costarc/MSXPi/documents/Tutorial - Setup  Raspberry Pi for MSXPi the Hard Way - Installing Raspbian from Scratch.pdf

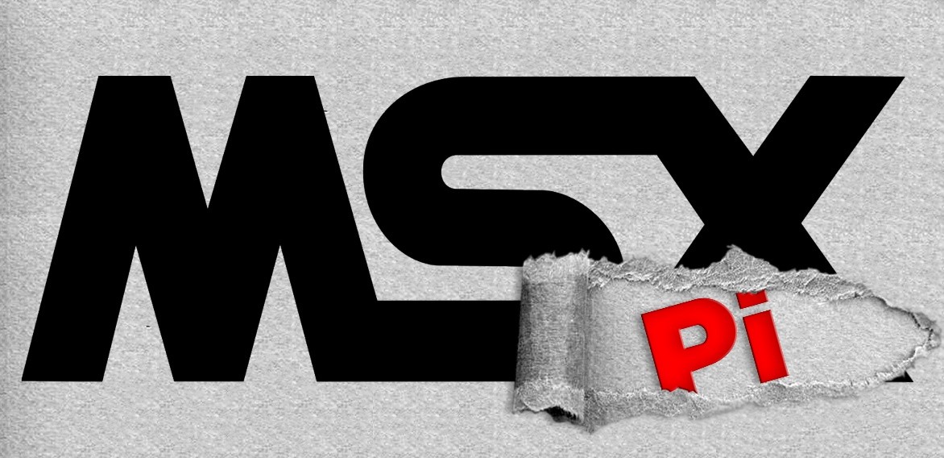
[picture p83: figure]

* This is a MSXPi Developer Contribution by Retropix Brazil * This tutorial will help you in a simple, direct and didactic way to prepare and install all the necessary software on the Micro SD card to use your MSXPi.

## Downloading the Installation Software for the Raspberry Pi OS

1st. Go to the link https://www.raspberrypi.com/software to download and run the software that will install the Raspberry Pi OS on your micro SD card.

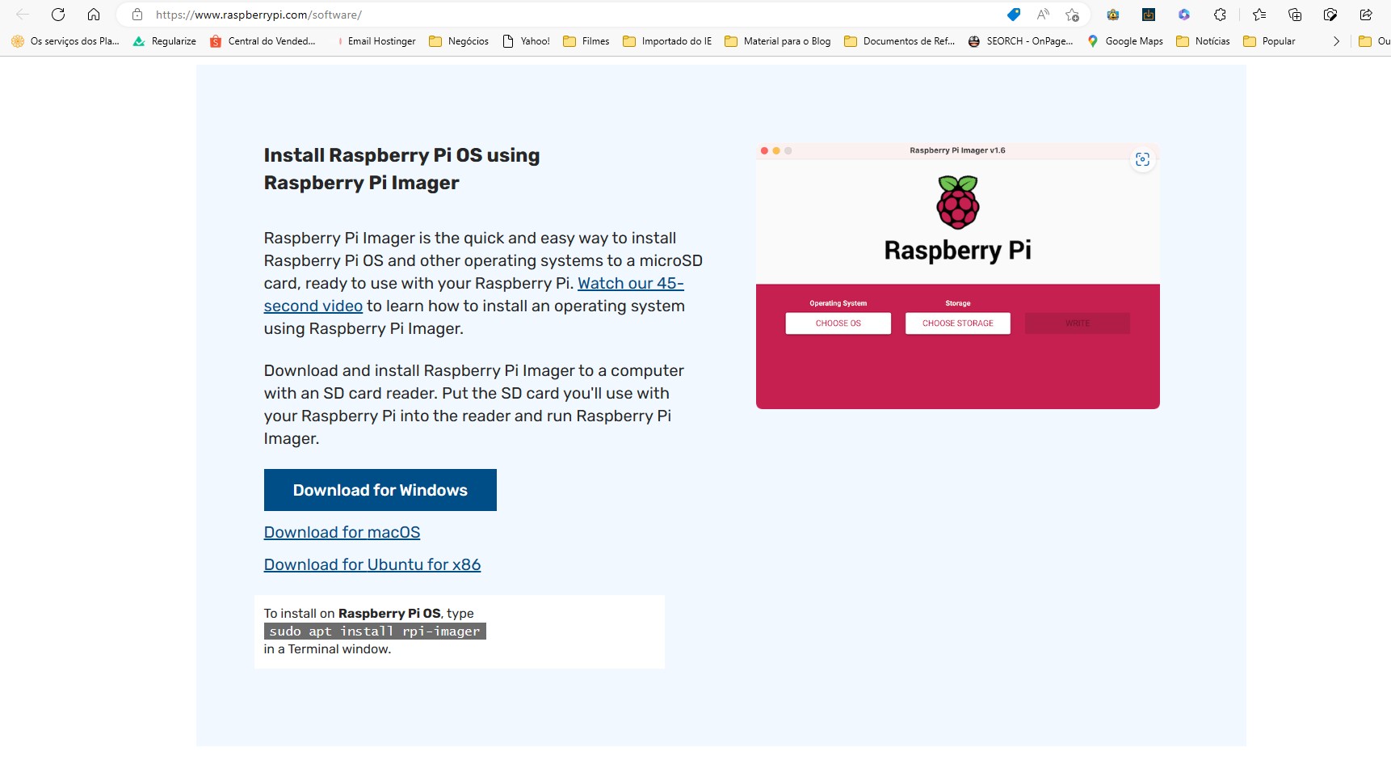
[picture p84: figure]

2nd. Download the installer for the platform that suits you best. The options are for Windows, macOS, and Ubuntu.
In this tutorial we will do the installation using Windows 10.
3rd. After downloading the imager_1.7.4.exe file (latest version) in your download area. Click on it to run.

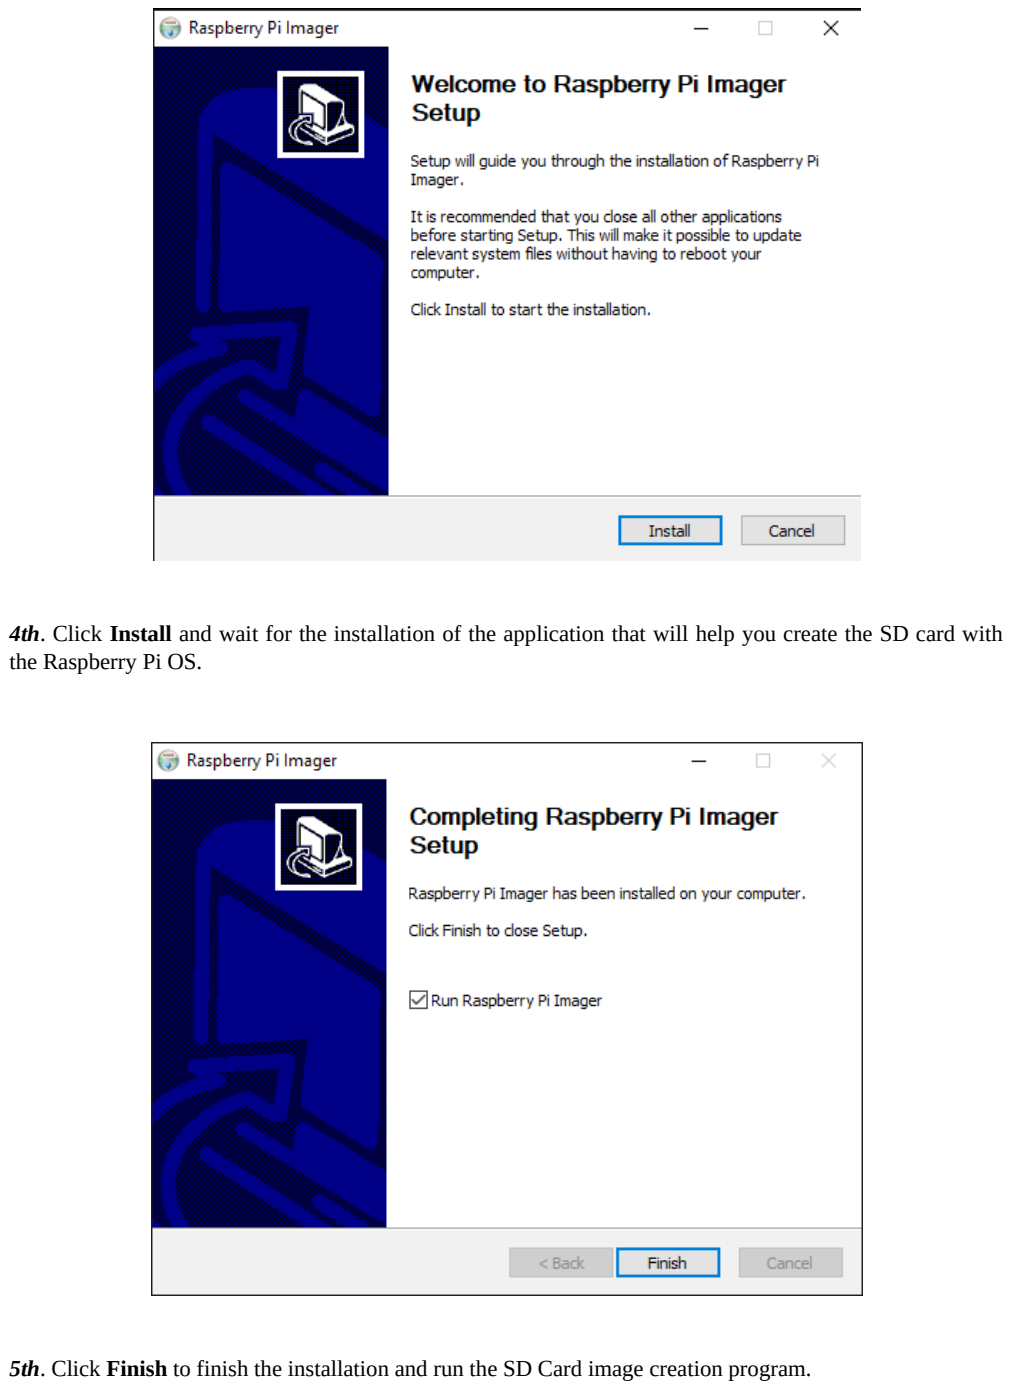
[picture p85: page 2]

4th. Click Install and wait for the installation of the application that will help you create the SD card with the Raspberry Pi OS.

5th. Click Finish to finish the installation and run the SD Card image creation program.

## Installing the Raspberry Pi OS System Properly

1st. Insert the Micro SD card you want to use into your Computer.

2nd. With the application open and the Micro SD card already inserted, first click on CHOOSE OS.


3rd. Choose the Raspberry Pi OS (Other) option to choose the version we use on the MSXPi.

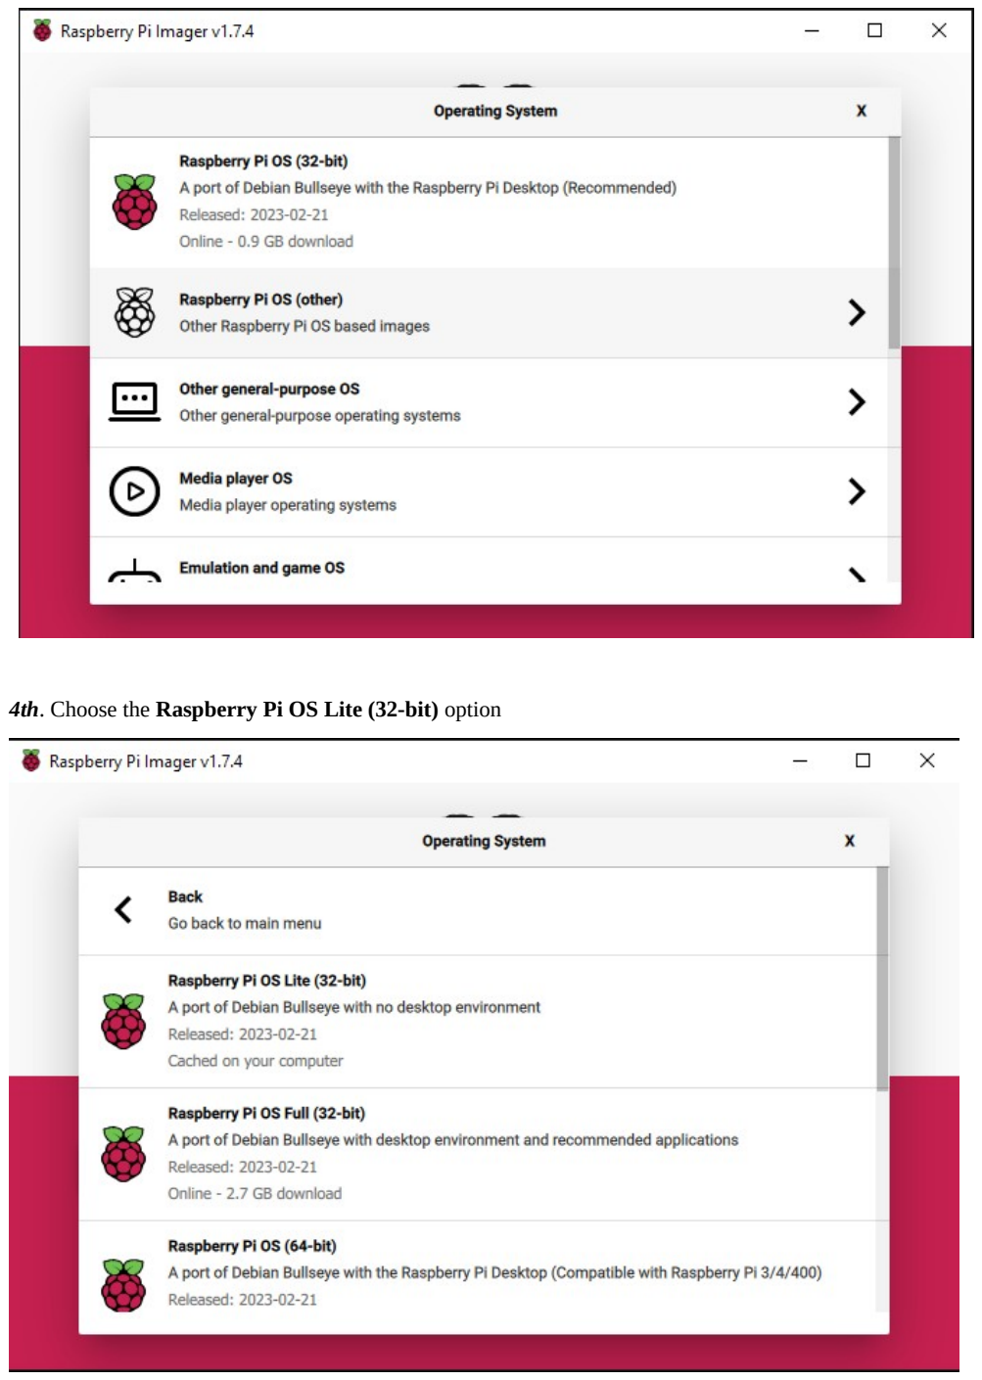
[picture p86: page 4]

4th. Choose the Raspberry Pi OS Lite (32-bit) option

5th. Now click on CHOOSE STORAGE button to choose your Micro SD card and install Raspberry Pi OS


6th. Click on the Gear button to configure the options for remote access in the Raspberry Pi OS via computer

7th. Check Set hostname

8th. Also check the option Enable SSH

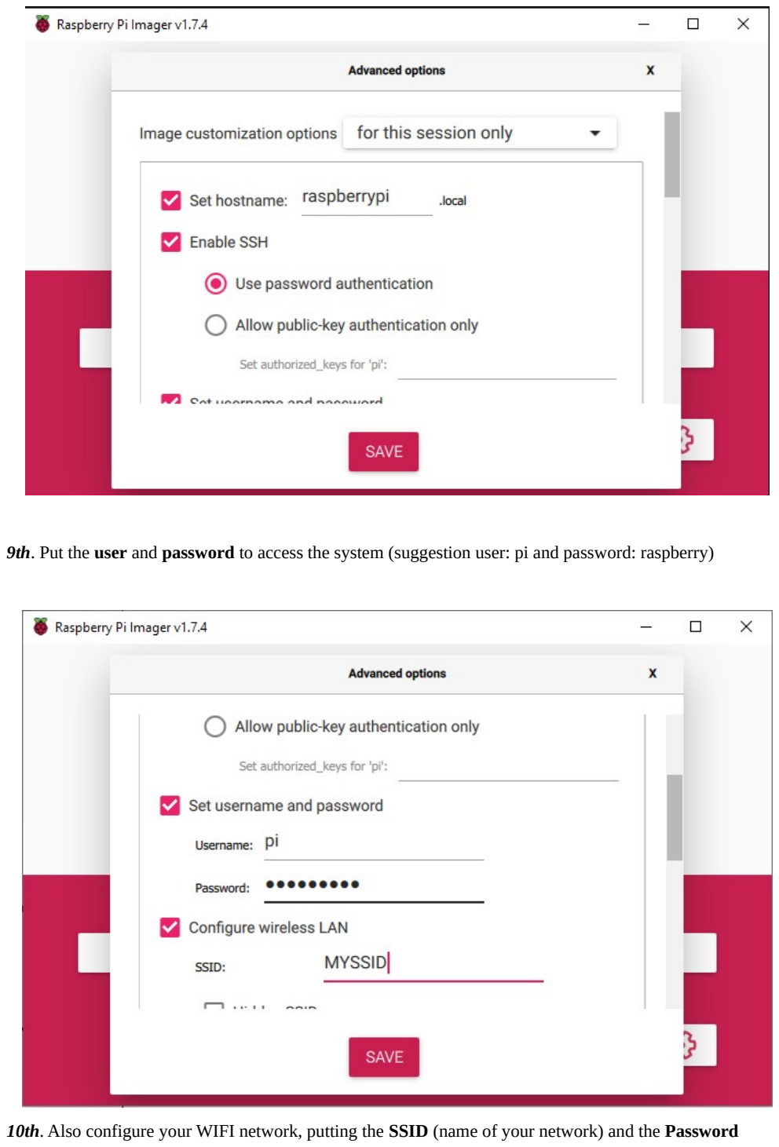
[picture p87: page 6]

9th. Put the user and password to access the system (suggestion user: pi and password: raspberry)

10th. Also configure your WIFI network, putting the SSID (name of your network) and the Password

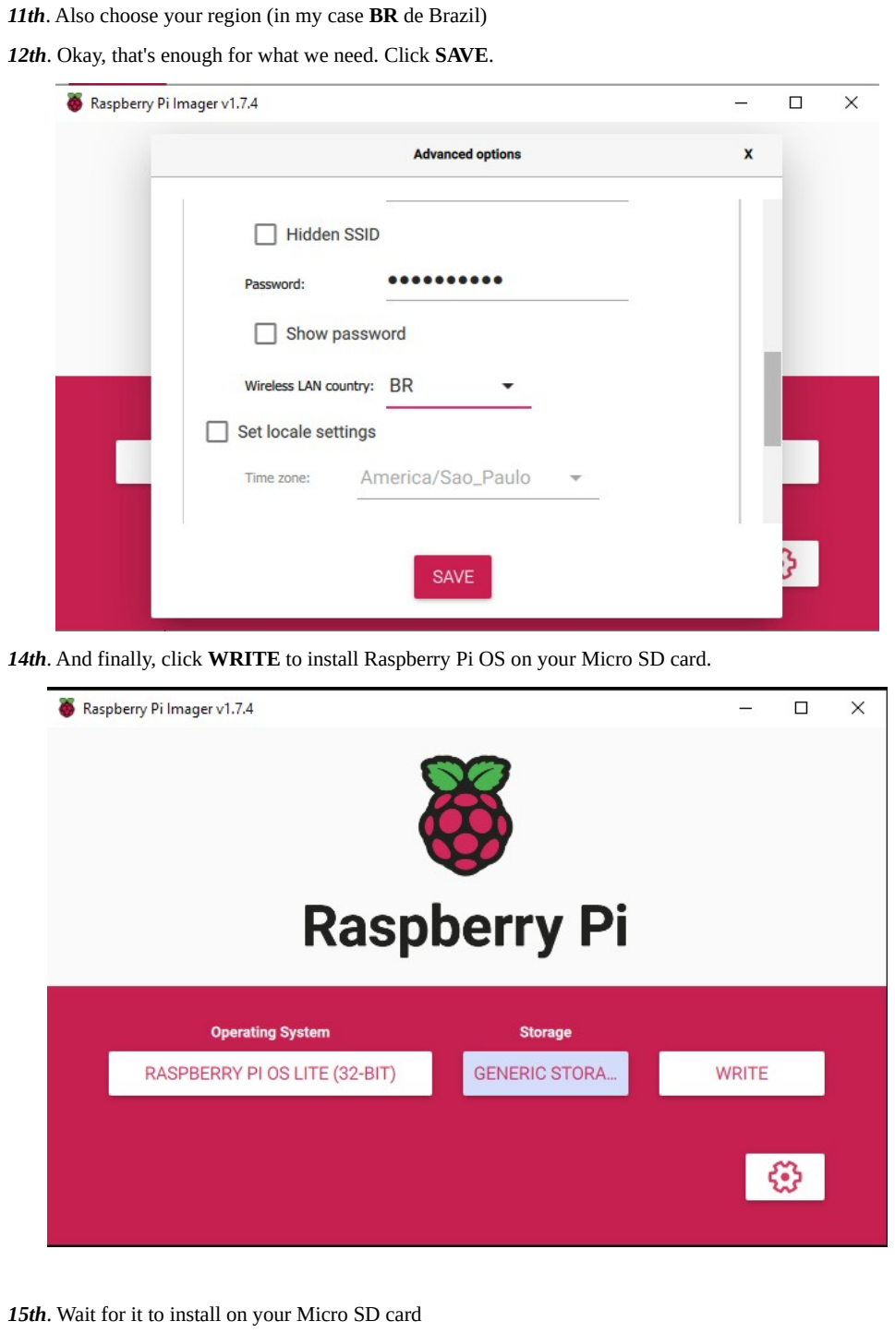
[picture p88: page 7]

11th. Also choose your region (in my case BR de Brazil) 12th. Okay, that's enough for what we need. Click SAVE.

14th. And finally, click WRITE to install Raspberry Pi OS on your Micro SD card.

15th. Wait for it to install on your Micro SD card

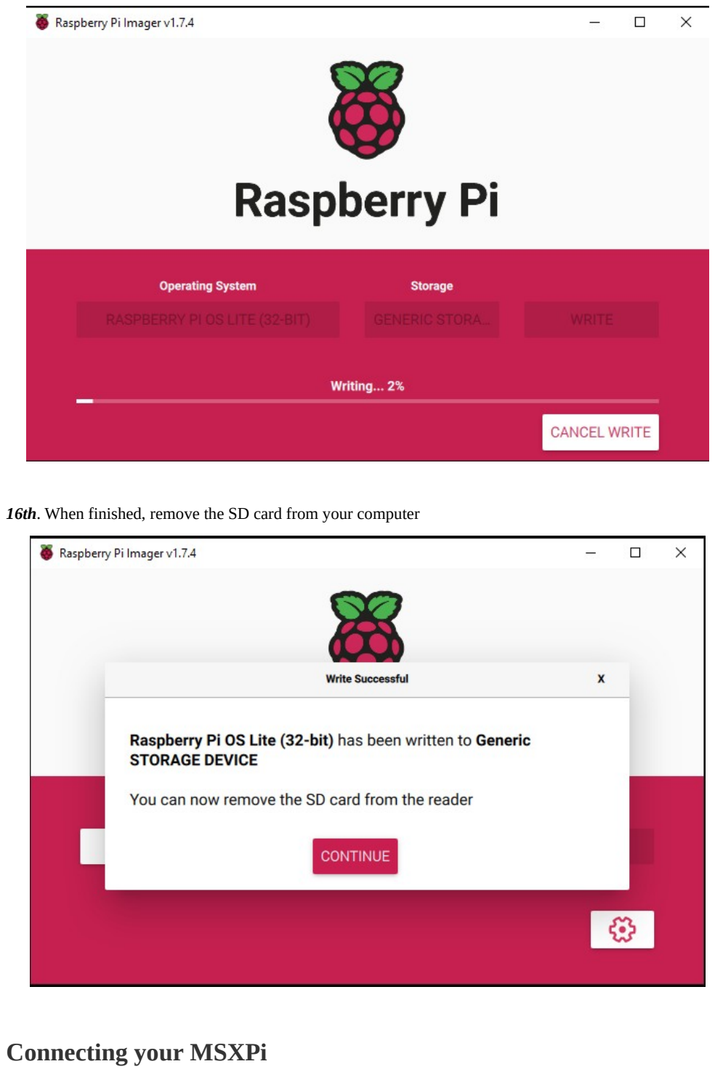
[picture p89: page 8]

16th. When finished, remove the SD card from your computer

## Connecting your MSXPi

Now, insert your Micro SD card into the MSXPi. Plug the MSXPi cartridge into your MSX and turn it on. Wait for all initialization to finish. At this point, MSXPi should be trying to connect to your WiFi network. After your MSXPi connects to your WiFi network (It takes a long time to connect to your network the first time, about 5-10 minutes). If you can, monitor your router by checking if the Raspberry has already connected or simply wait and test the connection through Putty.

When the SSH connection is already established, follow the next steps.

1st. Download (Download PuTTY - a free SSH and telnet client for Windows) (https://www.putty.org/) and install the Putty application if
you haven't already installed it on your computer. Putty is an SSH Client for Windows.

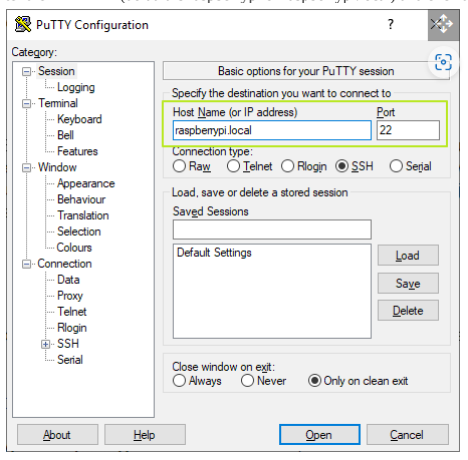
[picture p90: figure]

2nd. Run Putty, enter the hostname (default is raspberrypi or raspberrypi.local) and click the Open button.

3rd. Click Ok or Accept if you have any security alerts. This is not a problem.

4th. Enter your username (pi) and password (raspberrry).

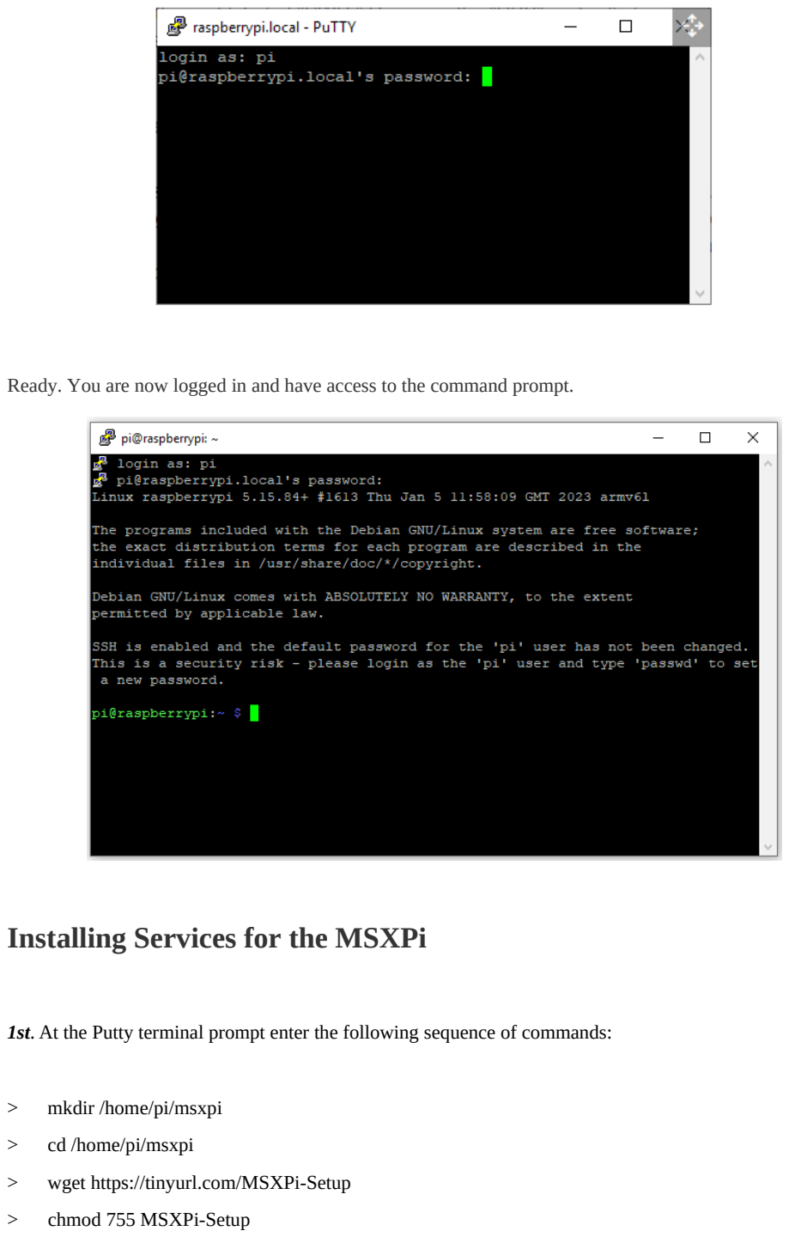
[picture p91: page 10]

Ready. You are now logged in and have access to the command prompt.

## Installing Services for the MSXPi

1st. At the Putty terminal prompt enter the following sequence of commands:

> | mkdir /home/pi/msxpi
> | cd /home/pi/msxpi
> | wget https://tinyurl.com/MSXPi-Setup
> | chmod 755 MSXPi-Setup

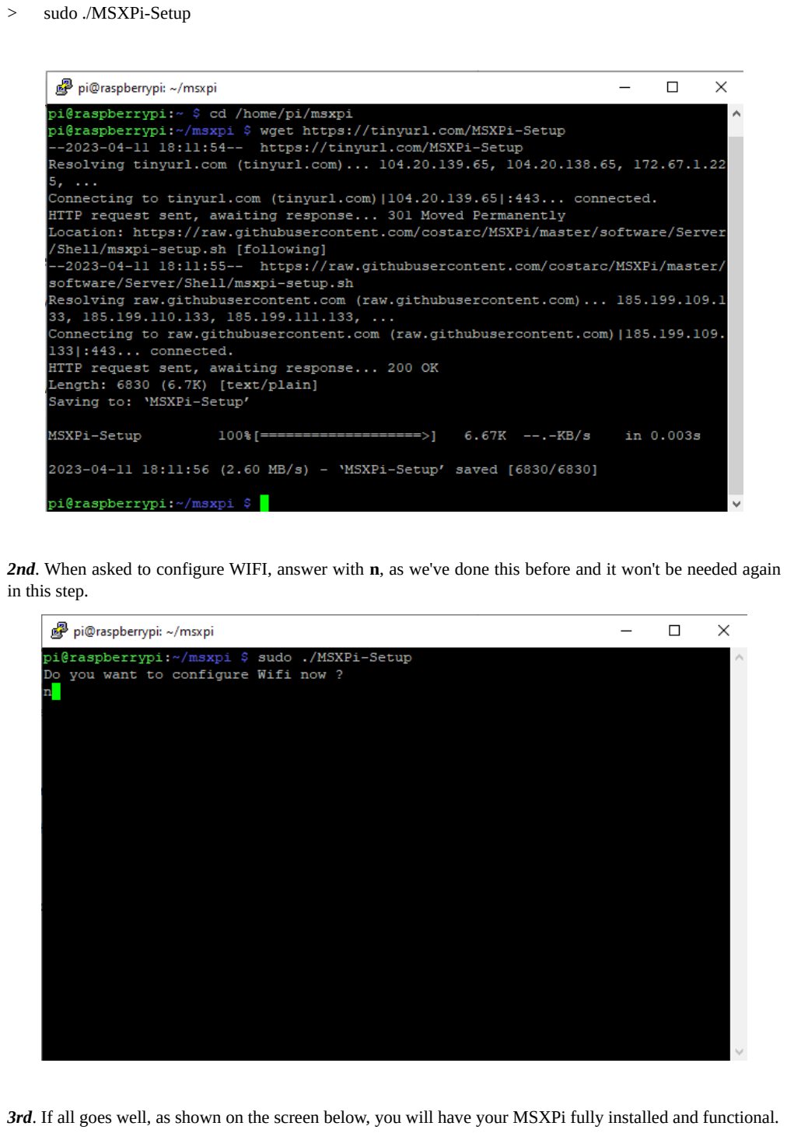
[picture p92: page 11]

> sudo ./MSXPi-Setup

2nd. When asked to configure WIFI, answer with n, as we've done this before and it won't be needed again in this step.

3rd. If all goes well, as shown on the screen below, you will have your MSXPi fully installed and functional.

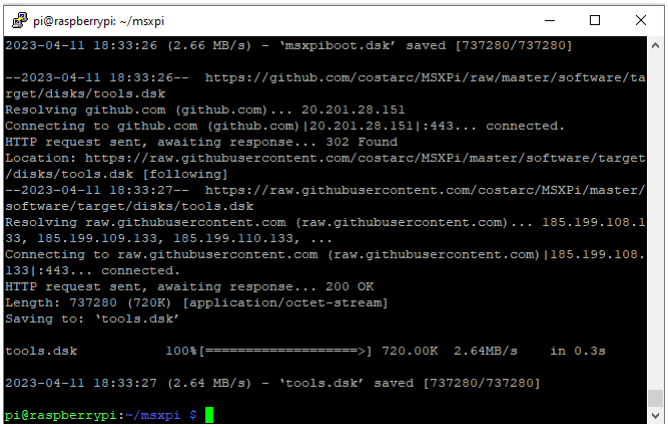
[picture p93: figure]

## References:

- Ton´s Harwares - How to Set Up a Headless Raspberry Pi, No Monitor Needed | Tom's Hardware
(tomshardware.com) (https://www.tomshardware.com/reviews/raspberry-pi-headless-setup-how-to,6028.html)
- Raspberry Pi - Raspberry Pi OS – Raspberry Pi (https://www.raspberrypi.com/software/)
- Putty - a free SSH and telnet client for Windows (https://www.putty.org/)

This document is part of the MSXPi project – by Ronivon Costa ( GitHub - costarc/MSXPi: Interface for MSX to Connect and use Raspberry Pi resources (https://github.com/costarc/MSXPi) )
