costarc/MSXPi/software/Server/Python/src/msxpi_pchess_irc.py

"""PCH1 IRC protocol: discovery in #msxpi, all game traffic private.

A room is the channel #pchess-<room> instead of #msxpi. Joining sends
PCH1 ROOM HELLO there; a free player answers PCH1 ROOM HERE (a busy one
answers PCH1 ROOM BUSY privately). On HELLO or HERE the player whose
folded nick sorts lower sends the usual private OFFER and so plays white;
in a room the OFFER is accepted at once. The game is then the same private
MOVE/ACK/DRAW/RESIGN exchange as a lobby match."""
import hashlib
import base64
import os
import queue
import re
import secrets
import socket
import ssl
import threading
import time
import chess

def fold(nick):
    return nick.lower().translate(str.maketrans('[]\\^','{}|~'))

def digest(board):
    return hashlib.sha256(board.fen().encode()).hexdigest()[:16]

# A SEEK or OFFER keeps a nick in the player list for ten minutes.
PLAYER_TTL=600


class Peer:
    def __init__(self,nick,send,room=None):
        self.nick=nick
        self.send=send
        self.room=room         # '#pchess-<room>' in a room, else None (lobby)
        self.board=chess.Board()
        self.peer=None
        self.match=None
        self.side=True
        self.phase='lobby'
        self.status='LOBBY'
        self.invite=None
        self.pending=None
        self.history=[]
        self.last_move=None
        self.players={}
        self.last_seek=-1000
        self.draw_offer=None   # 'me' or 'peer', until the one offered to moves
        self.result=None       # 'draw', or the colour (bool) that resigned

    def free(self):
        # A finished (or failed) match leaves the player free to seek, invite
        # or accept again without going back through the lobby (key 4).
        return self.phase=='lobby' or self.phase=='error' or             (self.phase=='playing' and self.over())

    def new_match(self):
        # Clear the old game only when the next one starts, so its final
        # position stays on screen until then.
        self.board=chess.Board()
        self.side=True
        self.pending=None
        self.history=[]
        self.last_move=None
        self.draw_offer=None
        self.result=None

    def channel(self):
        return self.room or '#msxpi'

    def announce_room(self):
        """Say HELLO in the room; the lower nick of a free pair then offers."""
        if not self.free(): raise ValueError('Already in a match')
        self.send(self.room,'PCH1 ROOM HELLO')
        self.status=('ROOM '+self.room[8:]+' - WAITING').upper()[:47]

    def room_pair(self,sender):
        if self.free() and fold(self.nick)<fold(sender):
            self.offer(sender)

    def seek(self):
        if self.room: raise ValueError('In a room; no lobby')
        if not self.free(): raise ValueError('Already in a match')
        if time.monotonic()-self.last_seek<60: raise ValueError('Wait before announcing again')
        self.send('#msxpi','PCH1 SEEK')
        self.last_seek=time.monotonic()
        self.status='SEEK SENT'

    def offer(self,nick):
        if not re.fullmatch(r'[A-Za-z][A-Za-z0-9_-]{0,15}',nick): raise ValueError('Invalid nickname')
        if not self.free() or fold(nick)==fold(self.nick): raise ValueError('Cannot challenge now')
        self.new_match()
        self.peer=nick
        self.match=secrets.token_hex(8)
        self.phase='offered'
        self.send(nick,f'PCH1 OFFER {self.match}')
        self.status='INVITE SENT'

    def accept(self):
        if not self.free() or not self.invite: raise ValueError('No invitation')
        self.new_match()
        self.peer,self.match=self.invite
        self.invite=None
        self.side=False
        self.phase='accepted'
        self.send(self.peer,f'PCH1 ACCEPT {self.match}')
        self.status='WAIT READY'

    def no_such_nick(self,nick):
        # An invite (or acceptance) to a missing player is abandoned; a game
        # in progress is left to the normal move retransmit and timeout.
        if self.peer and fold(nick)==fold(self.peer) and self.phase in ('offered','accepted'):
            self.peer=None; self.match=None; self.phase='lobby'
        self.status=(nick+': No such nick')[:47]
        for name in list(self.players):
            if fold(name)==fold(nick): del self.players[name]

    def seen(self,nick):
        for name in list(self.players):
            if fold(name)==fold(nick): del self.players[name]
        if len(self.players)>=64: self.players.pop(next(iter(self.players)))
        self.players[nick]=time.monotonic()

    def recent_players(self,max_age=PLAYER_TTL):
        """Nicks that announced themselves (SEEK or OFFER) lately, newest first."""
        now=time.monotonic()
        # seen() re-inserts a nick, so dict order is already oldest first.
        return [name for name,when in reversed(self.players.items())
                if now-when<max_age and fold(name)!=fold(self.nick)]

    def turn_status(self):
        # Whose colour is whose, from this player's point of view.
        colour='WHITE' if self.side else 'BLACK'
        if self.board.turn==self.side: return f'YOU ARE {colour} - YOUR MOVE'
        return f'YOU ARE {colour} - {self.peer} MOVES'

    def receive(self,sender,target,text):
        fields=text.split()
        if len(fields)<2 or fields[0]!='PCH1' or fold(sender)==fold(self.nick): return
        op=fields[1]
        if self.room and fold(target)==fold(self.room):
            if len(fields)==3 and op=='ROOM' and fields[2] in ('HELLO','HERE'):
                if fields[2]=='HELLO':
                    if self.free(): self.send(self.room,'PCH1 ROOM HERE')
                    else: self.send(sender,'PCH1 ROOM BUSY')
                self.room_pair(sender)
            return
        if fold(target)==fold('#msxpi'):
            if self.room: return
            if fields==['PCH1','SEEK'] and self.free():
                self.seen(sender)
                self.status='PLAYER '+sender+' WANTS TO PLAY'
            return
        if fold(target)!=fold(self.nick): return
        if op=='OFFER' and len(fields)==3 and re.fullmatch('[0-9a-f]{16}',fields[2]):
            self.seen(sender)
            if self.free():
                self.invite=(sender,fields[2])
                self.status='INVITE '+sender+' PRESS 7'
                if self.room: self.accept()
            return
        if op=='ROOM' and fields==['PCH1','ROOM','BUSY'] and self.room:
            if self.free() and self.phase!='playing':
                self.status='ROOM BUSY - GAME IN PROGRESS'
            return
        if not self.peer or fold(sender)!=fold(self.peer) or len(fields)<3 or fields[2]!=self.match: return
        if op=='ACCEPT' and len(fields)==3 and self.phase in ('offered','playing'):
            if self.phase=='offered': self.side=True; self.phase='playing'; self.status=self.turn_status()
            self.send(self.peer,f'PCH1 READY {self.match}')
        elif op=='READY' and len(fields)==3 and self.phase=='accepted':
            self.phase='playing'; self.status=self.turn_status()
        elif op=='MOVE' and len(fields)==7 and self.phase=='playing':
            if text==self.last_move:
                self.send(self.peer,f'PCH1 ACK {self.match} {fields[3]} {fields[6]}')
                return
            if self.result is not None or self.pending or self.board.turn==self.side: return
            if fields[3]!=str(len(self.board.move_stack)+1) or fields[5]!=digest(self.board):
                self.status='OUT OF SYNC'; self.phase='error'; return
            try: move=self.board.parse_uci(fields[4])
            except ValueError: return
            san=self.board.san(move)
            self.board.push(move)
            if digest(self.board)!=fields[6]:
                self.board.pop(); self.status='BAD POSITION'; self.phase='error'; return
            self.history.append(san)
            self.last_move=text
            if self.draw_offer=='me': self.draw_offer=None
            self.send(self.peer,f'PCH1 ACK {self.match} {fields[3]} {fields[6]}')
            self.status=self.turn_status()
        elif op=='DRAW' and len(fields)==3 and self.phase=='playing' and self.result is None:
            if self.draw_offer=='me': self.result='draw'
            else: self.draw_offer='peer'; self.status='OPPONENT OFFERS DRAW - ESC MENU'
        elif op=='RESIGN' and len(fields)==3 and self.phase=='playing' and self.result is None:
            self.result=not self.side
        elif op=='ACK' and len(fields)==5 and self.pending:
            if fields[3]==str(len(self.board.move_stack)) and fields[4]==digest(self.board):
                self.pending=None
                self.status=self.turn_status()

    def move(self,notation):
        if self.phase!='playing' or self.pending: raise ValueError('Waiting for peer')
        if self.board.turn!=self.side: raise ValueError('Opponent turn')
        if self.over(): raise ValueError('Game over')
        try: move=self.board.parse_uci(notation.lower().replace('-',''))
        except ValueError: move=self.board.parse_san(notation)
        before=digest(self.board)
        san=self.board.san(move)
        self.board.push(move)
        message=f'PCH1 MOVE {self.match} {len(self.board.move_stack)} {move.uci()} {before} {digest(self.board)}'
        try: self.send(self.peer,message)
        except Exception:
            self.board.pop(); raise
        self.history.append(san)
        if self.draw_offer=='peer': self.draw_offer=None
        self.pending=(message,time.monotonic(),0)
        self.status='WAIT ACK'

    def over(self):
        return self.result is not None or self.board.is_game_over(claim_draw=True)

    def draw(self):
        """Offer a draw on one's move, or accept the peer's offer.

        An offer lasts until the player it was made to moves, so a DRAW
        crossing a MOVE on the wire is read the same way by both sides."""
        if self.phase!='playing': raise ValueError('No game in progress')
        if self.over(): raise ValueError('Game over')
        if self.draw_offer!='peer' and self.board.turn!=self.side:
            raise ValueError('Offer a draw on your move')
        self.send(self.peer,f'PCH1 DRAW {self.match}')
        if self.draw_offer=='peer': self.result='draw'
        else: self.draw_offer='me'; self.status='DRAW OFFERED'

    def resign(self):
        if self.phase!='playing': raise ValueError('No game in progress')
        if self.over(): raise ValueError('Game over')
        self.send(self.peer,f'PCH1 RESIGN {self.match}')
        self.result=self.side

    def tick(self):
        if self.result is not None: self.pending=None
        if self.pending:
            message,sent,retries=self.pending
            if time.monotonic()-sent>=5:
                if retries>=3:
                    self.phase='error'; self.status='PEER TIMEOUT'; self.pending=None
                else:
                    self.send(self.peer,message)
                    self.pending=(message,time.monotonic(),retries+1)

    def snapshot(self):
        board=self.board
        status=self.status
        outcome=board.outcome(claim_draw=True)
        if self.invite and self.free():
            pass   # a new invite outranks the last game's result
        elif outcome:
            status='DRAW' if outcome.winner is None else 'WHITE WINS' if outcome.winner else 'BLACK WINS'
        elif self.result=='draw': status='DRAW AGREED'
        elif self.result is not None:
            status='WHITE RESIGNED - BLACK WINS' if self.result else 'BLACK RESIGNED - WHITE WINS'
        elif board.is_check() and self.phase=='playing' and not self.pending:
            status='WHITE CHECK' if board.turn else 'BLACK CHECK'
        return dict(board=''.join(board.piece_at(chess.square(x,7-y)).symbol()
            if board.piece_at(chess.square(x,7-y)) else '.' for y in range(8) for x in range(8)),
            turn=int(board.turn),side=int(not self.side),over=bool(outcome) or self.result is not None,
            matched=self.phase=='playing',opponent=self.peer or '',
            status=status[:47],history=self.history[-12:],ply=len(board.move_stack))


def tls_context():
    """System CAs plus certifi's bundle when installed.

    Some system stores (the Microsoft Store Python on Windows, OpenSSL 3.0)
    build an expired path for Let's Encrypt's 2026 chain; certifi's bundle
    lets verification find the valid one. Verification stays on."""
    context=ssl.create_default_context()
    try:
        import certifi
        context.load_verify_locations(certifi.where())
    except (ImportError,OSError):
        pass
    return context


class IRC:
    def __init__(self,config=None,room=None):
        config=config or {}
        self.nick=os.environ.get('PCHESS_IRC_NICK') or config.get('IRCNICK') or 'pch'+secrets.token_hex(2)
        if not re.fullmatch(r'[A-Za-z][A-Za-z0-9_-]{0,15}',self.nick): raise ValueError('Invalid lobby nickname (IRCNICK)')
        host=os.environ.get('PCHESS_IRC_HOST') or config.get('IRCADDR') or 'irc.libera.chat'
        self.account=config.get('IRCACCOUNT','')
        self.password=config.get('IRCPASSWORD','')
        if bool(self.account)!=bool(self.password):
            raise ValueError('Set both IRCACCOUNT and IRCPASSWORD')
        if any(c in self.account+self.password for c in '\x00\r\n'):
            raise ValueError('Invalid lobby account (IRCACCOUNT)')
        self.authenticated=False
        self.auth_phase='cap' if self.account else 'none'
        port=int(os.environ.get('PCHESS_IRC_PORT') or config.get('PCHESSIRCPORT') or '6697')
        tls_value=os.environ.get('PCHESS_IRC_TLS') or config.get('IRCTLS') or ('0' if port==6667 else '1')
        tls=tls_value.lower() in ('1','true','yes','on')
        if self.account and not tls:
            raise ValueError('Lobby login requires TLS')
        sock=socket.create_connection((host,port),timeout=5)
        try:
            if tls:
                sock=tls_context().wrap_socket(sock,server_hostname=host)
        except ssl.SSLCertVerificationError as exc:
            sock.close()
            print('PCHESS IRC TLS '+str(exc),flush=True)
            raise ValueError('Lobby certificate error') from None
        except Exception:
            sock.close(); raise
        self.sock=sock
        self.lock=threading.Lock()
        self.messages=queue.Queue(256)
        self.error=None
        self.closed=False
        self.ready=False
        self.started=time.monotonic()
        self.peer=Peer(self.nick,self.message,room)
        self.peer.status='ACCESSING LOBBY'
        if self.account: self.line('CAP REQ :sasl')
        self.line(f'NICK {self.nick}')
        self.line(f'USER {self.nick} 0 * :MSXPi PChess')
        threading.Thread(target=self.reader,daemon=True).start()

    def line(self,line):
        if '\r' in line or '\n' in line or len(line)>450: raise ValueError('Invalid lobby message')
        with self.lock: self.sock.sendall((line+'\r\n').encode('ascii'))

    def message(self,target,text):
        if not self.ready: raise ValueError('Lobby not ready; wait')
        self.line(f'PRIVMSG {target} :{text}')
        if os.environ.get('PCHESS_IRC_TRACE')=='1':
            print(f'PCHESS IRC TX {target} :{text}',flush=True)

    def reader(self):
        buffer=b''
        try:
            while True:
                try: data=self.sock.recv(4096)
                except socket.timeout: continue
                if not data: raise ConnectionError('Lobby disconnected')
                buffer+=data
                if len(buffer)>16384: raise ValueError('Lobby message too large')
                while b'\n' in buffer:
                    raw,buffer=buffer.split(b'\n',1)
                    line=raw.decode('utf-8','replace').rstrip('\r')
                    if line.startswith('@'): line=line.split(' ',1)[1]
                    if line.startswith('PING '): self.line('PONG '+line[5:]); continue
                    parts=line.split(' ',3)
                    if self.authenticate(line,parts): continue
                    if line.startswith('ERROR '): raise ConnectionError(line[:150])
                    if len(parts)>1 and parts[1]=='001':
                        if self.account and not self.authenticated:
                            raise ValueError('Lobby login not confirmed')
                        self.nick=parts[2]
                        self.peer.nick=self.nick
                        self.peer.status='JOINING ROOM' if self.peer.room else 'JOINING LOBBY'
                        self.line('JOIN '+self.peer.channel())
                    if len(parts)>2 and parts[1]=='JOIN' and fold(parts[0][1:].split('!',1)[0])==fold(self.nick) and fold(parts[2].lstrip(':'))==fold(self.peer.channel()):
                        self.ready=True
                        self.peer.status='LOBBY '+self.nick
                        if self.peer.room: self.announce=True
                    if len(parts)>3 and parts[1]=='401':
                        # Unknown nickname: report it but stay in the lobby.
                        self.peer.no_such_nick(parts[3].partition(' :')[0].strip())
                        continue
                    if len(parts)>1 and parts[1] in ('403','404','432','464','465','471','473','474','475','477','489'):
                        if parts[1]=='477':
                            raise ValueError('Lobby account login required (477)')
                        # ":srv 401 me bob :No such nick/channel" -> "bob: No such nick/channel"
                        params,_,text=(parts[3] if len(parts)>3 else '').partition(' :')
                        subject=params.strip()
                        raise ValueError(((subject+': ' if subject else '')+(text or 'Lobby error '+parts[1]))[:140])
                    if len(parts)>1 and parts[1]=='433': raise ValueError('Lobby nickname in use')
                    if len(parts)==4 and parts[1]=='PRIVMSG' and parts[3].startswith(':PCH1 '):
                        item=(parts[0][1:].split('!',1)[0],parts[2],parts[3][1:])
                        if os.environ.get('PCHESS_IRC_TRACE')=='1':
                            print('PCHESS IRC RX '+' '.join(item),flush=True)
                        try: self.messages.put_nowait(item)
                        except queue.Full: pass
        except Exception as exc:
            self.error=None if getattr(self,'closed',False) else str(exc)
            if self.error and os.environ.get('PCHESS_IRC_TRACE')=='1':
                print('PCHESS IRC ERROR '+self.error,flush=True)
        finally:
            self.password=''
            self.sock.close()

    def authenticate(self,line,parts):
        """SASL PLAIN over verified TLS; never send credentials to chat/logs."""
        if not self.account: return False
        if len(parts)>3 and parts[1]=='CAP':
            command=parts[3].split(' ',1)[0]
            if command=='NAK': raise ValueError('Lobby server does not support login')
            if command=='ACK' and self.auth_phase=='cap':
                caps=parts[3].split(':',1)[-1].split()
                if not any(c.split('=',1)[0]=='sasl' for c in caps):
                    raise ValueError('Lobby login not acknowledged')
                self.auth_phase='challenge'
                self.peer.status='LOBBY LOGIN'
                self.line('AUTHENTICATE PLAIN')
            return True
        auth_parts=line.split(' ')
        if auth_parts[0].startswith(':'): auth_parts=auth_parts[1:]
        challenge=len(auth_parts)==2 and auth_parts[0]=='AUTHENTICATE' and auth_parts[1].lstrip(':')=='+'
        if challenge and self.auth_phase=='challenge':
            payload=base64.b64encode(('\0'+self.account+'\0'+self.password).encode('utf-8')).decode('ascii')
            self.password=''
            for pos in range(0,len(payload),400):
                self.line('AUTHENTICATE '+payload[pos:pos+400])
            if len(payload)%400==0: self.line('AUTHENTICATE +')
            self.auth_phase='result'
            return True
        if len(parts)>1 and parts[1]=='903' and self.auth_phase=='result':
            self.authenticated=True
            self.auth_phase='done'
            self.line('CAP END')
            return True
        if len(parts)>1 and parts[1] in ('902','904','905','906','907','908'):
            raise ValueError('Lobby login failed '+parts[1])
        return False

    def poll(self):
        if self.error: raise ValueError(self.error)
        if not self.ready and time.monotonic()-self.started>60:
            self.close()
            raise ValueError('Lobby connection timed out')
        if getattr(self,'announce',False):
            self.announce=False
            self.peer.announce_room()
        while not self.messages.empty(): self.peer.receive(*self.messages.get_nowait())
        self.peer.tick()
        return self.peer.snapshot()

    def close(self):
        self.closed=True
        try: self.sock.shutdown(socket.SHUT_RDWR)
        except OSError: pass
        self.sock.close()
